davidnnaji/Server-Rack-Shelf/Server Rack Shelf/Photos/IMG_8182.jpg

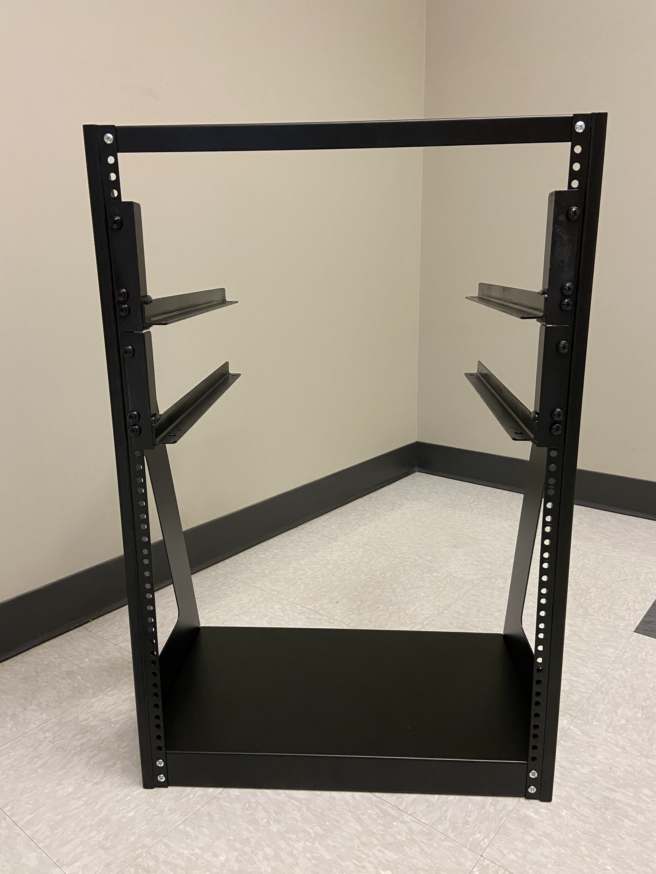
Server Rack Shelf/Photos/IMG_8182.jpg
