davidnnaji/Server-Rack-Shelf/Server Rack Shelf/Photos/IMG_8199.jpg

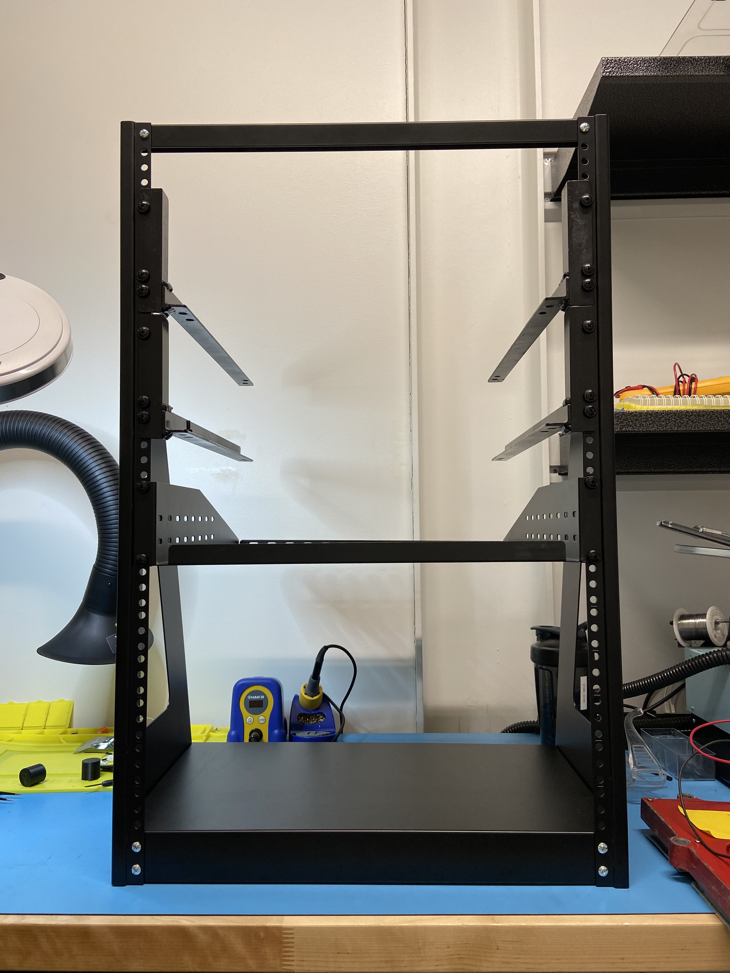
Server Rack Shelf/Photos/IMG_8199.jpg
