davidnnaji/Server-Rack-Shelf/Server Rack Shelf/Parts/ECU Server Rack Parts/3RU Angle Iron.SLDPRT

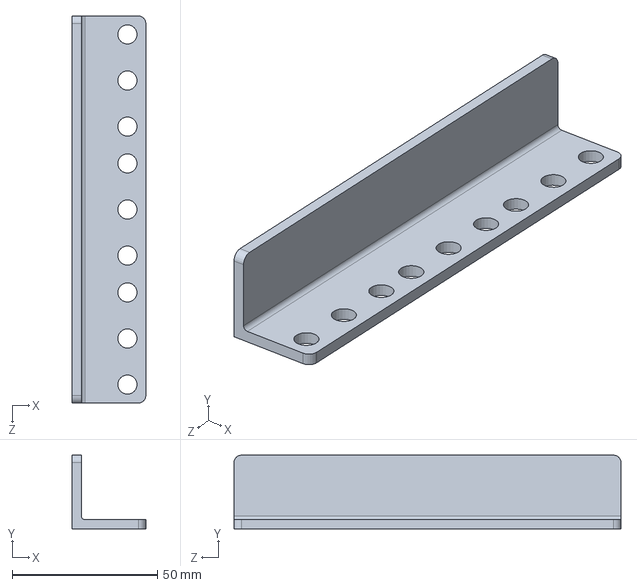
[picture p24: CAD file, 2021-03-02]
Server Rack Shelf/Parts/ECU Server Rack Parts/3RU Angle Iron.SLDPRT
25.4 x 25.4 x 133.4 mm
