davidnnaji/Server-Rack-Shelf/General Purpose Display/Parts/v2/DARPADisplay-Board-v2.SLDPRT

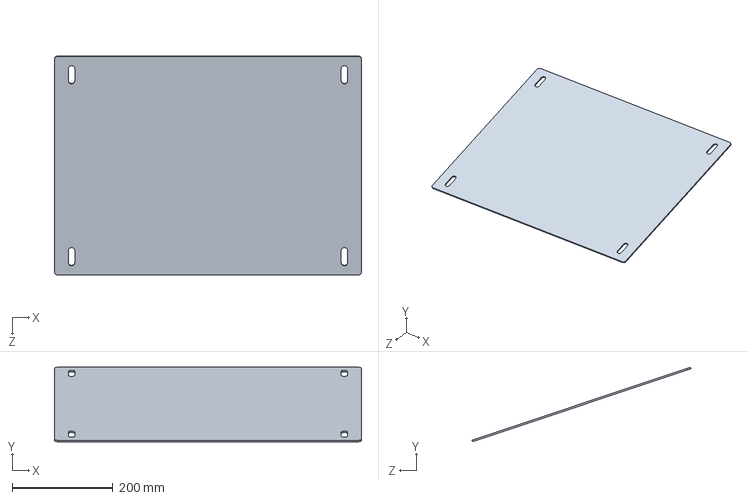
[picture p25: CAD file, 2020-12-21]
General Purpose Display/Parts/v2/DARPADisplay-Board-v2.SLDPRT
609.6 x 148.1 x 434.6 mm
