davidnnaji/Server-Rack-Shelf/Server Rack Shelf/Parts/ECU Server Rack Parts/Long Angle Iron.SLDPRT

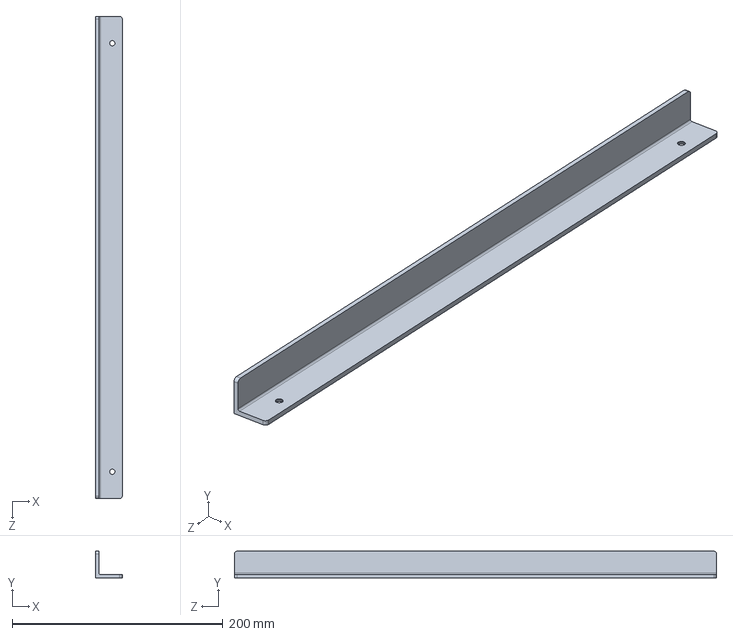
[picture p26: CAD file, 2021-03-02]
Server Rack Shelf/Parts/ECU Server Rack Parts/Long Angle Iron.SLDPRT
25.4 x 25.4 x 457.2 mm
