davidnnaji/Server-Rack-Shelf/Server Rack Shelf/Parts/ECU Server Rack Parts/Baseboard.SLDPRT

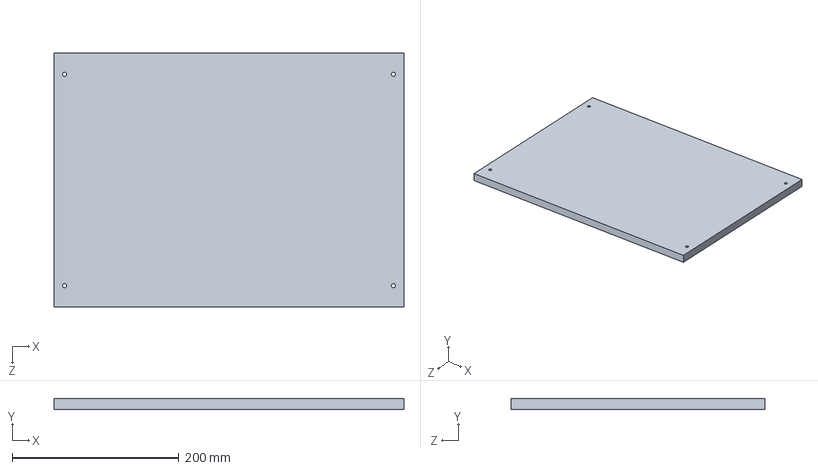
[picture p27: CAD file, 2021-03-02]
Server Rack Shelf/Parts/ECU Server Rack Parts/Baseboard.SLDPRT
420.4 x 12.7 x 304.8 mm
