davidnnaji/Server-Rack-Shelf/Server Rack Shelf/Photos/IMG_8169.JPG

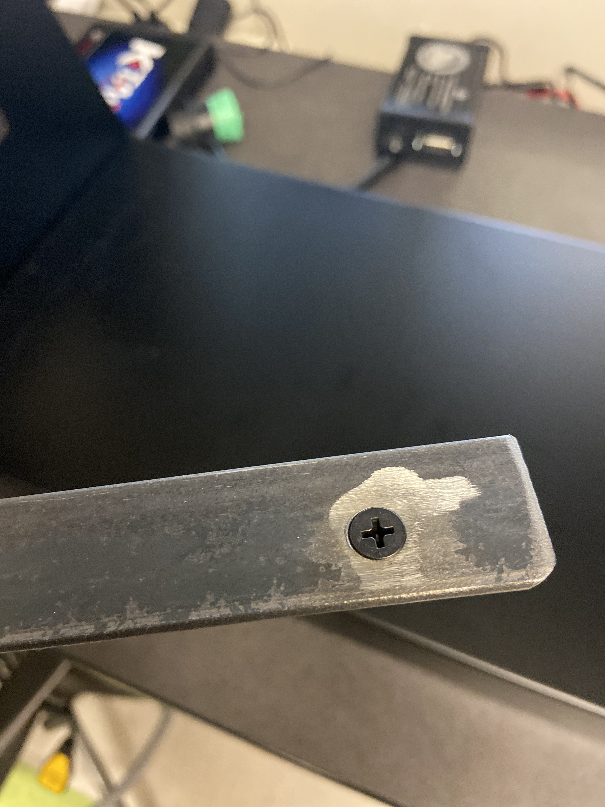
Server Rack Shelf/Photos/IMG_8169.JPG
