davidnnaji/Server-Rack-Shelf/Server Rack Shelf/Photos/IMG_8196.jpg

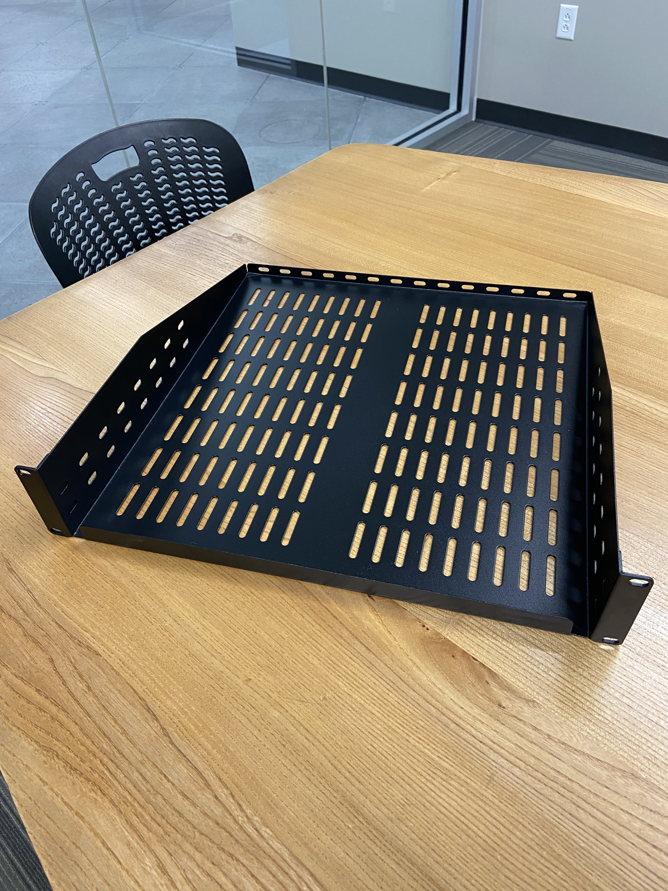
Server Rack Shelf/Photos/IMG_8196.jpg
