davidnnaji/Server-Rack-Shelf/Server Rack Shelf/Photos/IMG_8201.jpg

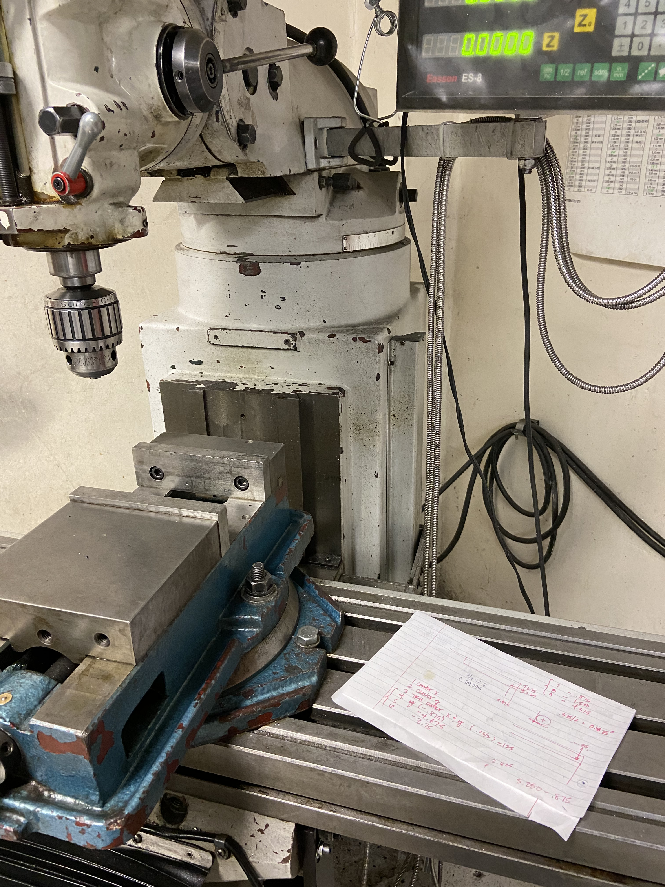
Server Rack Shelf/Photos/IMG_8201.jpg
